GEIGEIGEIST/KLOR/case/acrylic/saegewerk/README.md

# KLOR SAEGEWERK ACRYLIC CASE FILES 

If you want to use the KLOR wireless (through ZMK) you need to choose the bluetooth case. If you plan on using it wired (through QMK) you should choose the regular case. The differences are a cutout for a JST connector in the bottom plate and another one for the ON/OFF switch in the side of the case.\

> **Note**
> You need a switchplate, no matter what case you choose.

[saegewerk](/case/acrylic/saegewerk/regular/)
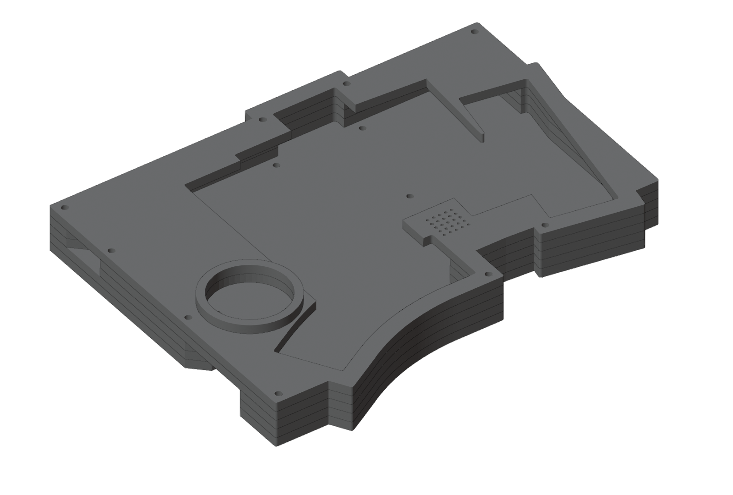
[picture p25: case/docs/images/saegewerk_acryl_ble.png]
saegewerk bluetooth
[](/case/acrylic/saegewerk/bluetooth/)
