GEIGEIGEIST/KLOR/case/3DP/konrad/bluetooth/README.md

# KLOR KONRAD 3DP BLE CASE

You can choose a case with or without support for the SplitKB tenting puck.\
The 3DP cases I use were printed in PA-12-HP Nylon (MJF) by [JLCPCB](https://jlcpcb.com/).

konrad
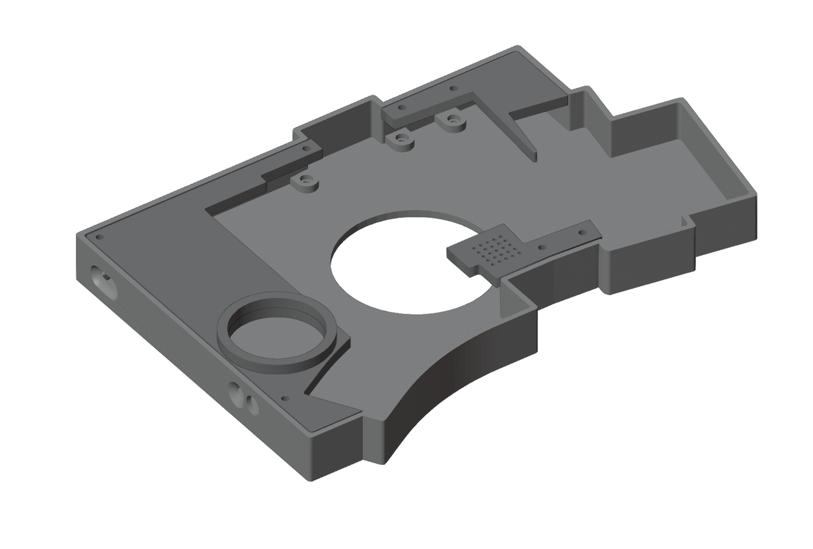
[picture p35: case/docs/images/konrad_3dp_ble_puck.png]
konrad puck
