GEIGEIGEIST/KLOR/case/3DP/konrad/regular/README.md

# KLOR KONRAD 3DP CASE

You can choose a case with or without support for the SplitKB tenting puck.\
The 3DP cases I use were printed in PA-12-HP Nylon (MJF) by [JLCPCB](https://jlcpcb.com/).

konrad
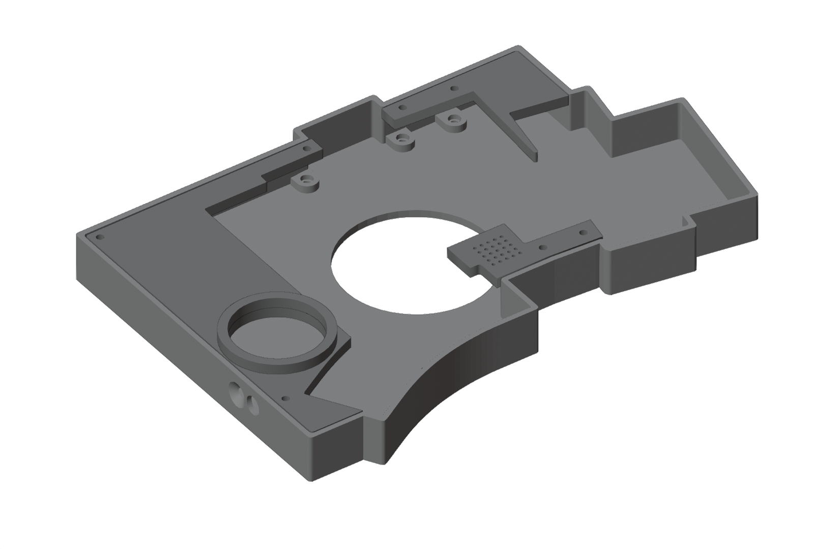
[picture p36: case/docs/images/konrad_3dp_puck.png]
konrad puck
