GEIGEIGEIST/KLOR/case/3DP/polydactyl/regular/README.md

# KLOR POLYDACTYL 3DP CASE

You can choose a case with or without support for the SplitKB tenting puck.\
The 3DP cases I use were printed in PA-12-HP Nylon (MJF) by [JLCPCB](https://jlcpcb.com/).

polydactyl
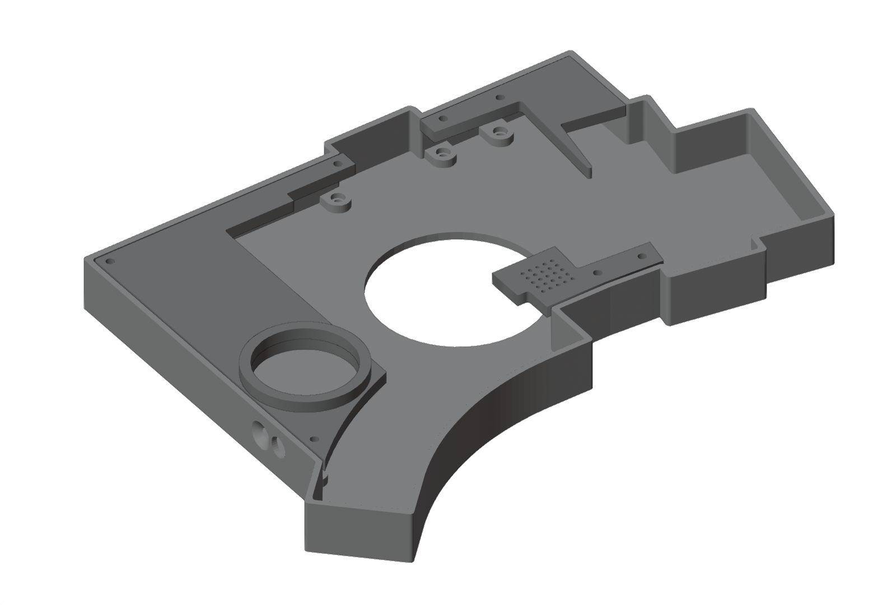
[picture p38: case/docs/images/polydactyl_3dp_puck.png]
polydactyl puck
