GEIGEIGEIST/KLOR/case/3DP/saegewerk/regular/README.md

# KLOR SAEGEWERK 3DP CASE

You can choose a case with or without support for the SplitKB tenting puck.\
The 3DP cases I use were printed in PA-12-HP Nylon (MJF) by [JLCPCB](https://jlcpcb.com/).

saegewerk
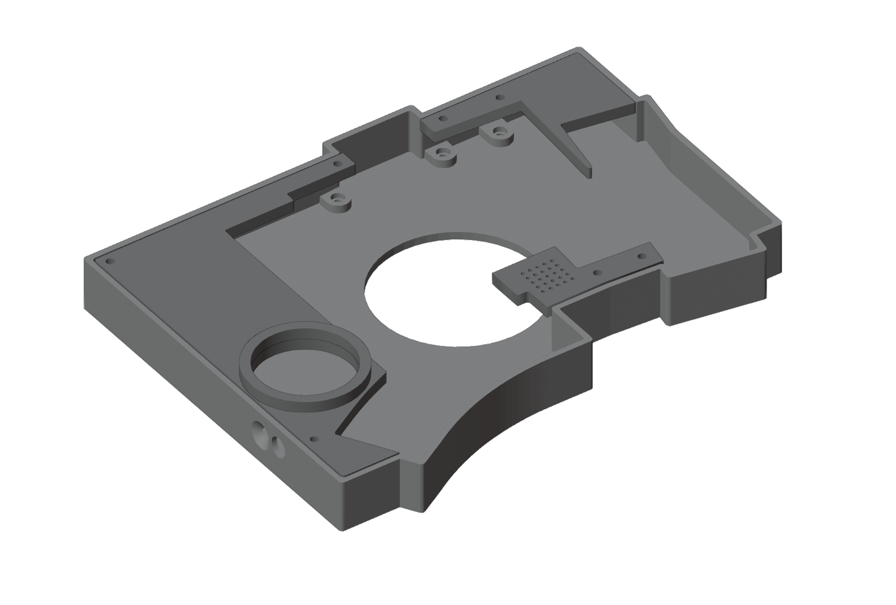
[picture p40: case/docs/images/saegewerk_3dp_puck.png]
saegewerk puck
