GEIGEIGEIST/KLOR/case/3DP/yubitsume/bluetooth/README.md

# KLOR YUBITSUME 3DP BLE CASE

You can choose a case with or without support for the SplitKB tenting puck.\
The 3DP cases I use were printed in PA-12-HP Nylon (MJF) by [JLCPCB](https://jlcpcb.com/).

yubitsume
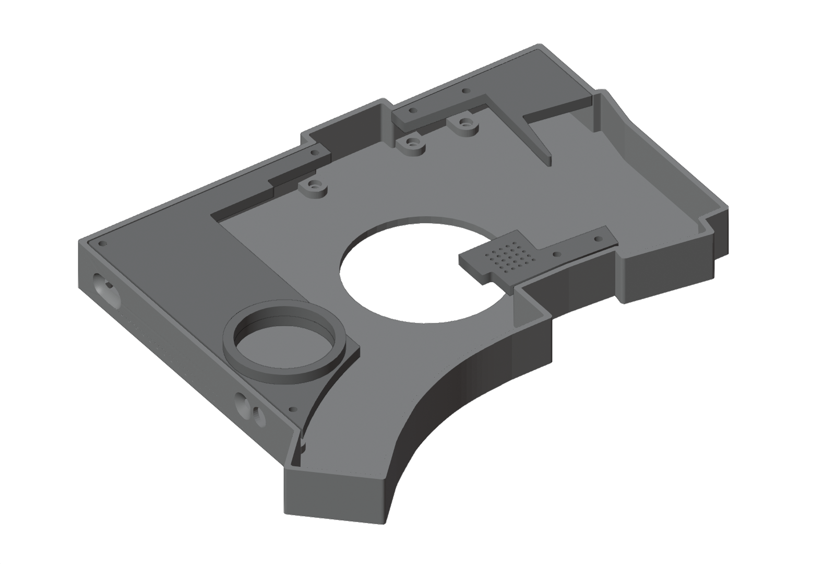
[picture p41: case/docs/images/yubitsume_3dp_ble_puck.png]
yubitsume puck
