GEIGEIGEIST/KLOR/case/3DP/yubitsume/regular/README.md

# KLOR YUBITSUME 3DP CASE

You can choose a case with or without support for the SplitKB tenting puck.\
The 3DP cases I use were printed in PA-12-HP Nylon (MJF) by [JLCPCB](https://jlcpcb.com/).

yubitsume
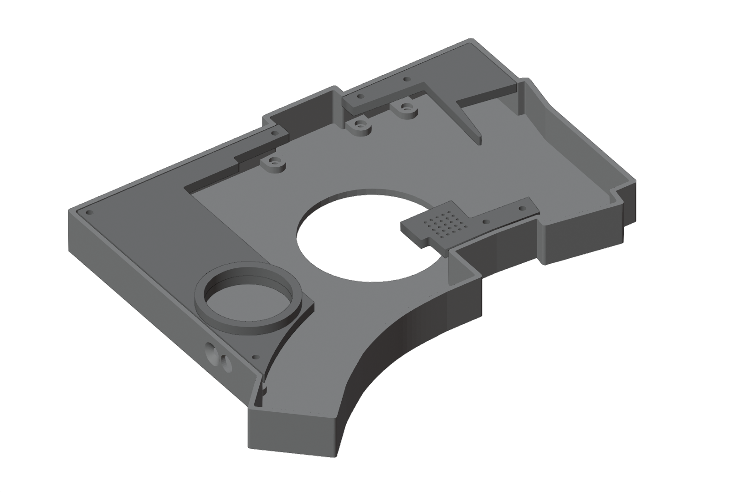
[picture p42: case/docs/images/yubitsume_3dp_puck.png]
yubitsume puck
