GEIGEIGEIST/KLOR/case/3DP/yubitsume/switchplate/KLOR_yubitsume_3DP_switchplate.step

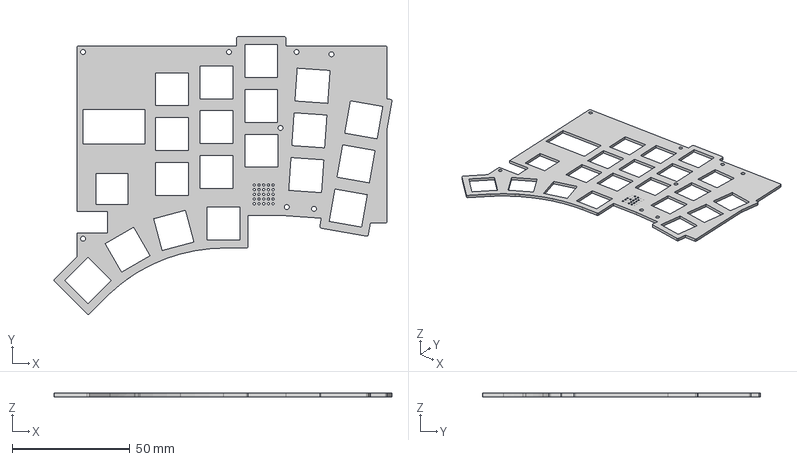
[picture p57: CAD file, 2022-08-15]
case/3DP/yubitsume/switchplate/KLOR_yubitsume_3DP_switchplate.step
143.8 x 118.2 x 1.50 mm
