GEIGEIGEIST/KLOR/case/3DP/polydactyl/acrylic/KLOR_polydactyl_3DPcase_acrylic_logotype.dxf

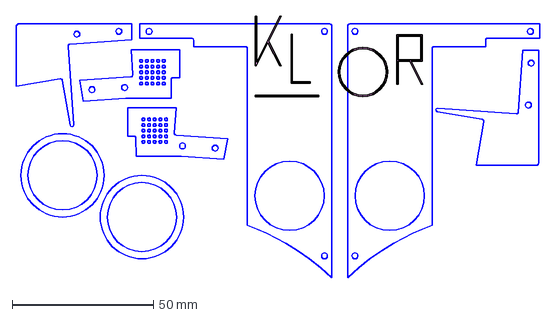
[picture p60: CAD file, 2022-08-22]
case/3DP/polydactyl/acrylic/KLOR_polydactyl_3DPcase_acrylic_logotype.dxf
185.0 x 92.4 mm
