GEIGEIGEIST/KLOR/case/3DP/saegewerk/acrylic/KLOR_saegewerk_3DPcase_acrylic_logotype.dxf

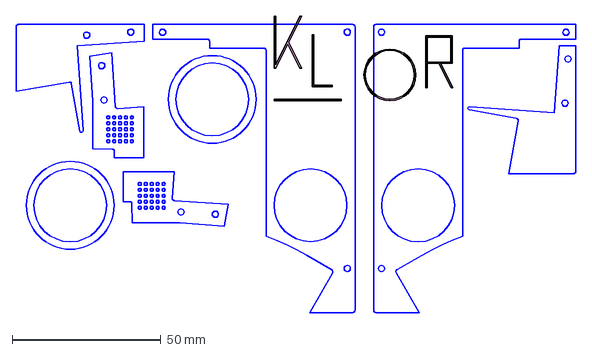
[picture p61: CAD file, 2022-08-22]
case/3DP/saegewerk/acrylic/KLOR_saegewerk_3DPcase_acrylic_logotype.dxf
188.1 x 99.5 mm
