GEIGEIGEIST/KLOR/case/3DP/yubitsume/acrylic/KLOR_yubitsume_3DPcase_acrylic.dxf

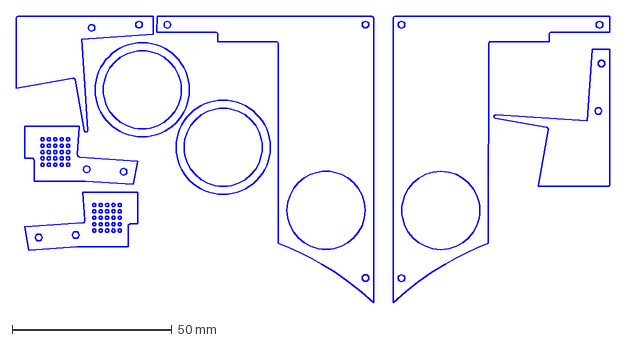
[picture p62: CAD file, 2022-08-22]
case/3DP/yubitsume/acrylic/KLOR_yubitsume_3DPcase_acrylic.dxf
186.0 x 89.7 mm
