GEIGEIGEIST/KLOR/case/3DP/yubitsume/bluetooth/KLOR_yubitsume_case_puck_ble_L.stl

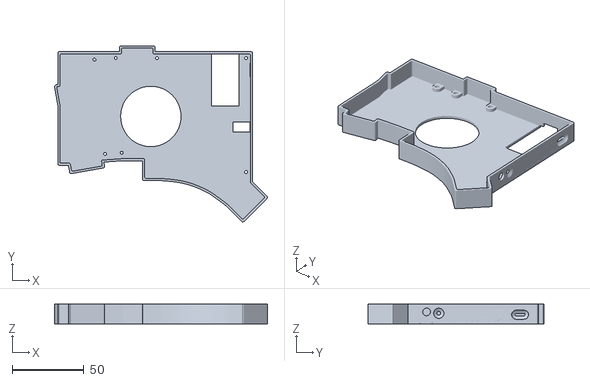
[picture p63: CAD file, 2022-09-01]
case/3DP/yubitsume/bluetooth/KLOR_yubitsume_case_puck_ble_L.stl
148.4 x 122.7 x 13.6
