GEIGEIGEIST/KLOR/docs/images/buildguide/cutouts.png

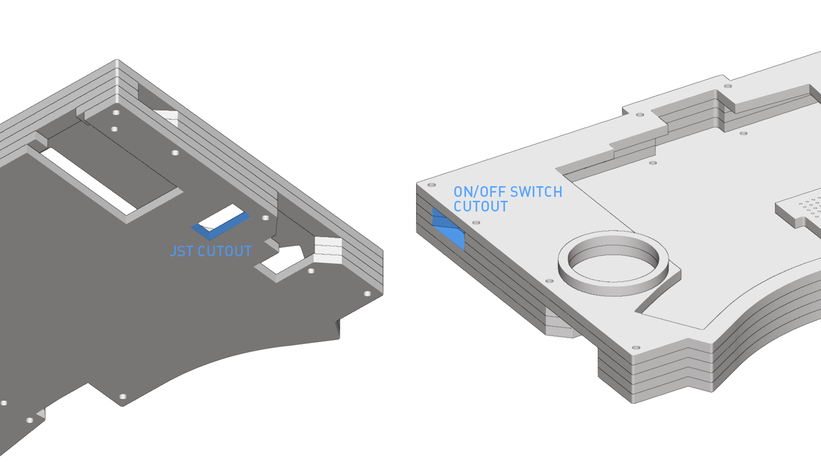
docs/images/buildguide/cutouts.png
